Sandpiper131/Sand-Ortholinear-Keyboard/QMKDEVBRD/Keypad v1/keypad.sch

## EAGLE design QMKDEVBRD/Keypad v1/keypad.sch (2021-04-14)

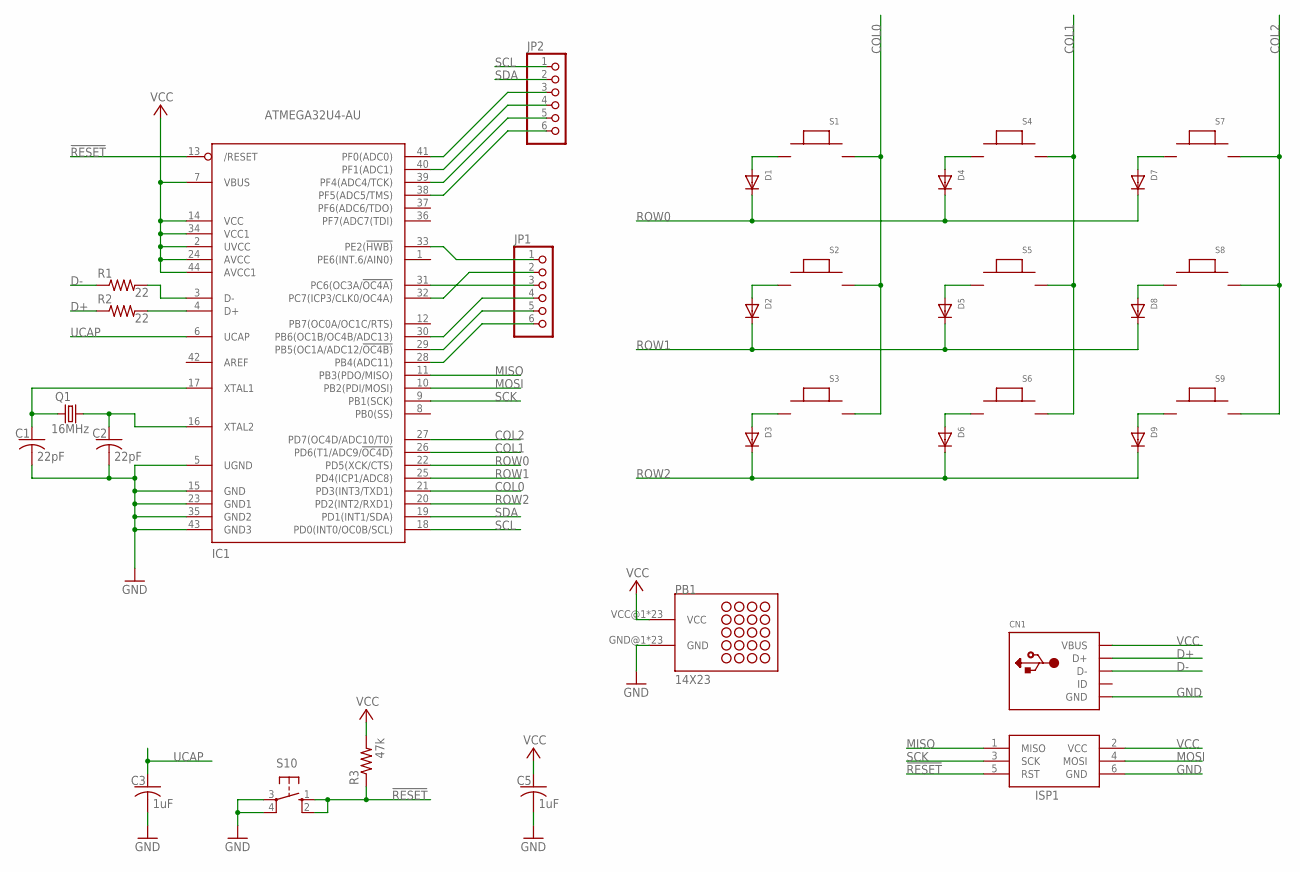
[picture p12: schematic keypad.sch]

Parts:
C1, C2: 22pF; C0805
C3, C5: 1uF; C0805
CN1: USBMOLEX; USB-MINIB-THM-MOLEX
D1, D2, D3, D4, D5, D6, D7, D8, D9: DIODESOD-123; SOD-123
IC1: ATMEGA32U4-AU; TQFP44
ISP1: AVRISP-6; AVRISP
JP1, JP2: PINHD-1X6; 1X06
PB1: 14X23
Q1: 16MHz; HC49/S
R1, R2: 22; R0805
R3: 47k; R0805
S1, S2, S3, S4, S5, S6, S7, S8, S9: MX-SMD; MX_SMD
S10: 10-XX; B3F-10XX

Connections:
!RESET: IC1.13 (/RESET), ISP1.5 (RST), R3.1, S10.1 (S), S10.2 (S1)
COL0: IC1.21 (PD3(INT3/TXD1)), S1.P$2, S2.P$2, S3.P$2
COL1: IC1.26 (PD6(T1/ADC9/!OC4D)), S4.P$2, S5.P$2, S6.P$2
COL2: IC1.27 (PD7(OC4D/ADC10/T0)), S7.P$2, S8.P$2, S9.P$2
D+: CN1.D+, R2.1
D-: CN1.D-, R1.1
GND: C1.2, C2.2, C3.2, C5.2, CN1.GND, IC1.5 (UGND), IC1.15 (GND), IC1.23 (GND1), IC1.35 (GND2), IC1.43 (GND3), ISP1.6 (GND), PB1.GND@1 (GND), S10.3, S10.4 (P1)
MISO: IC1.11 (PB3(PDO/MISO)), ISP1.1 (MISO)
MOSI: IC1.10 (PB2(PDI/MOSI)), ISP1.4 (MOSI)
unnamed: D4.A, S4.P$1
unnamed: D5.A, S5.P$1
unnamed: D1.A, S1.P$1
unnamed: D2.A, S2.P$1
unnamed: IC1.3 (D-), R1.2
unnamed: IC1.4 (D+), R2.2
unnamed: D7.A, S7.P$1
unnamed: D9.A, S9.P$1
unnamed: D8.A, S8.P$1
unnamed: D6.A, S6.P$1
unnamed: D3.A, S3.P$1
PB4: IC1.28 (PB4(ADC11)), JP1.6
PB5: IC1.29 (PB5(OC1A/ADC12/!OC4B)), JP1.5
PB6: IC1.30 (PB6(OC1B/OC4B/ADC13)), JP1.4
PC6: IC1.31 (PC6(OC3A/!OC4A)), JP1.3
PC7: IC1.32 (PC7(ICP3/CLK0/OC4A)), JP1.2
PE2: IC1.33 (PE2(!HWB)), JP1.1
PF0: IC1.41 (PF0(ADC0)), JP2.3
PF1: IC1.40 (PF1(ADC1)), JP2.4
PF4: IC1.39 (PF4(ADC4/TCK)), JP2.5
PF5: IC1.38 (PF5(ADC5/TMS)), JP2.6
ROW0: D1.C, D4.C, D7.C, IC1.22 (PD5(XCK/CTS))
ROW1: D2.C, D5.C, D8.C, IC1.25 (PD4(ICP1/ADC8))
ROW2: D3.C, D6.C, D9.C, IC1.20 (PD2(INT2/RXD1))
SCK: IC1.9 (PB1(SCK)), ISP1.3 (SCK)
SCL: IC1.18 (PD0(INT0/OC0B/SCL)), JP2.1
SDA: IC1.19 (PD1(INT1/SDA)), JP2.2
UCAP: C3.1, IC1.6 (UCAP)
VCC: C5.1, CN1.VBUS, IC1.2 (UVCC), IC1.7 (VBUS), IC1.14 (VCC), IC1.24 (AVCC), IC1.34 (VCC1), IC1.44 (AVCC1), ISP1.2 (VCC), PB1.VCC@1 (VCC), R3.2
XTAL1: C1.1, IC1.17 (XTAL1), Q1.1
XTAL2: C2.1, IC1.16 (XTAL2), Q1.2
